septentrio-gnss/TeenG5/Pictures/board.png

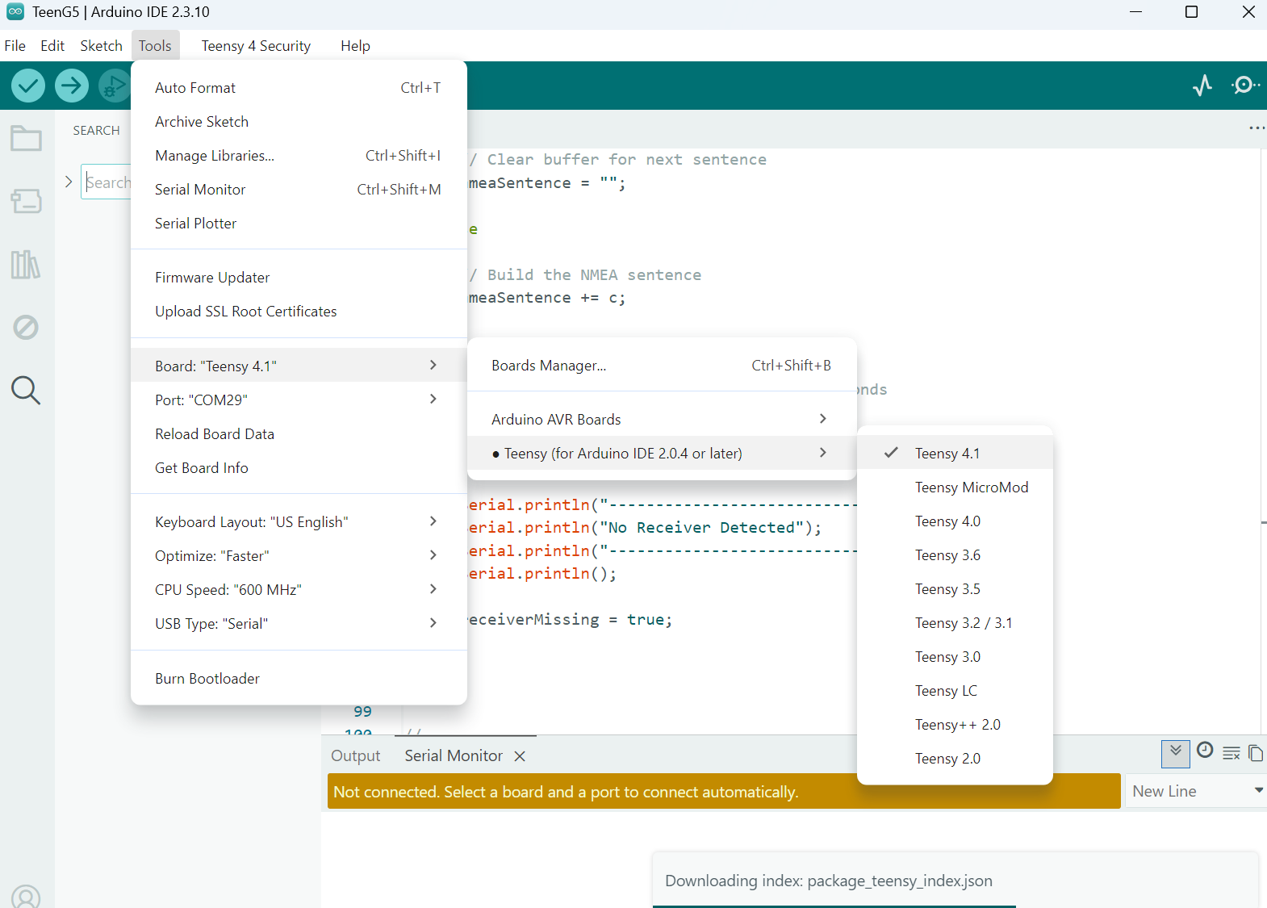
Pictures/board.png
